jcpst/loop_switcher/hardware/loop_switcher/loop_switcher.kicad_sch

## KiCad design hardware/loop_switcher/loop_switcher.kicad_sch (2025-12-18)

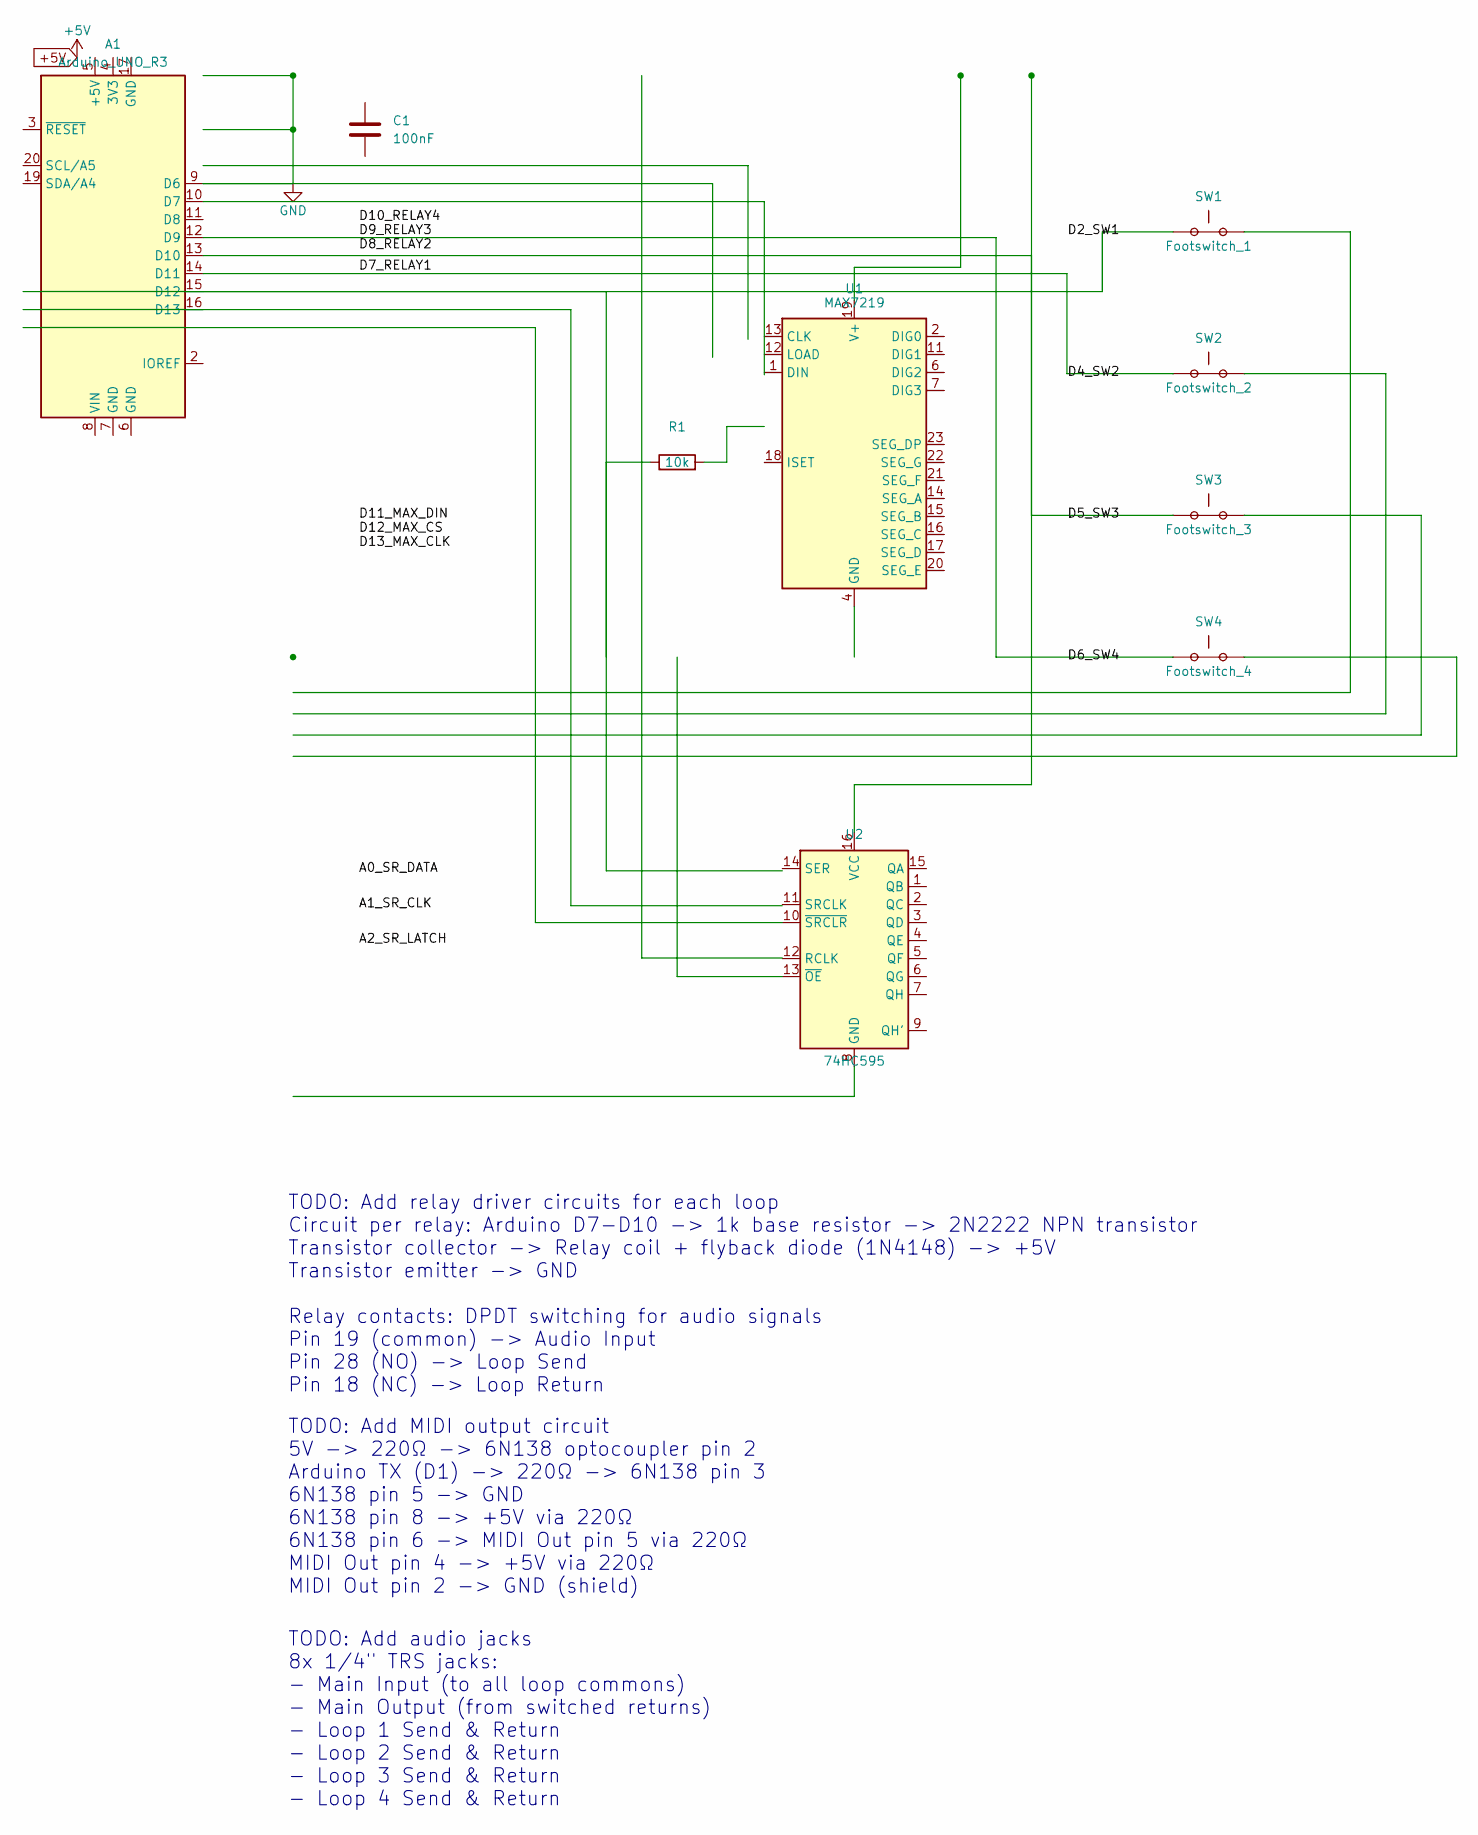
[picture p3: schematic loop_switcher.kicad_sch]

Parts:
A1: Arduino_UNO_R3
C1: 100nF
R1: 10k
SW1: Footswitch_1
SW2: Footswitch_2
SW3: Footswitch_3
SW4: Footswitch_4
U1: MAX7219
U2: 74HC595

Connections:
D4_SW2: A1.14 (D11)
D5_SW3: A1.13 (D10)
D6_SW4: A1.12 (D9)
GND: A1.9 (D6)

Notes on the sheet:
TODO: Add relay driver circuits for each loop Circuit per relay: Arduino D7-D10 -> 1k base resistor -> 2N2222 NPN transistor Transistor collector -> Relay coil + flyback diode (1N4148) -> +5V Transistor emitter -> GND Relay contacts: DPDT switching for audio signals Pin 19 (common) -> Audio Input P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
TODO: Add MIDI output circuit 5V -> 220Ω -> 6N138 optocoupler pin 2 Arduino TX (D1) -> 220Ω -> 6N138 pin 3 6N138 pin 5 -> GND 6N138 pin 8 -> +5V via 220Ω 6N138 pin 6 -> MIDI Out pin 5 via 220Ω MIDI Out pin 4 -> +5V via 220Ω MIDI Out pin 2 -> GND (shield)
TODO: Add audio jacks 8x 1/4" TRS jacks: - Main Input (to all loop commons) - Main Output (from switched returns) - Loop 1 Send & Return - Loop 2 Send & Return - Loop 3 Send & Return - Loop 4 Send & Return
