jcpst/loop_switcher/src/display.h

#ifndef DISPLAY_H
#define DISPLAY_H

#include <Arduino.h>
#include <LedControl.h>

// Number of digits in the display
#define DISPLAY_DIGITS 8

enum DisplayState {
  SHOWING_MANUAL,
  SHOWING_BANK,
  FLASHING_PC,
  SHOWING_SAVED,
  EDIT_MODE_ANIMATED
};

class Display {
public:
  Display(uint8_t dinPin, uint8_t clkPin, uint8_t csPin);

  void begin();
  void update(DisplayState state, uint8_t value, const bool loopStates[4], bool globalPreset = false, uint8_t animFrame = 0);
  void displayBankNumber(uint8_t num, bool globalPreset = false);
  void displayChannel(uint8_t ch);
  void displayManualStatus(const bool loopStates[4]);
  void displayEdit(uint8_t animFrame);
  void displaySaved(uint8_t animFrame);
  void clear();

private:
  LedControl lc;
  
  // Display buffers to track current state
  // Store both the character value and a type flag to distinguish between chars and digits
  uint8_t digitBuffer[DISPLAY_DIGITS];      // Current values on display (char ASCII or digit 0-15)
  bool isDigitBuffer[DISPLAY_DIGITS];       // True if position contains a digit, false if char
  bool decimalBuffer[DISPLAY_DIGITS];       // Current decimal point states
  bool bufferInitialized;                   // Track if buffer has been initialized
  
  void setCharAt(uint8_t position, char c);
  void setCharAtBuffered(uint8_t position, char c, bool dp);
  void setDigitAtBuffered(uint8_t position, uint8_t digit, bool dp);
  void clearBuffered();
};

#endif
